green-codes/fst-01/fst-01.sch

## KiCad design fst-01.sch (2018-08-16, an earlier design)

Schematic: fst-01.sch

Parts:
C1, C2: 27pF
C3, C4, C5, C6, C7, C11: 0.1uF
C8, C10: 4.7uF
C9: 0.01uF
D1: LED
J1: USB_A
K1: CONN_3
K2, K3: CONN_2
R1: 510
U1: STM32F103TB
U2: CAT6217-330
U3: NUF2221W1
U4: SST25VF032B
X1: 12MHz
